0xceejay/2wd-diff-drive-bot/src/bot_description/meshes/tt_motor_3777_v10__3.stl

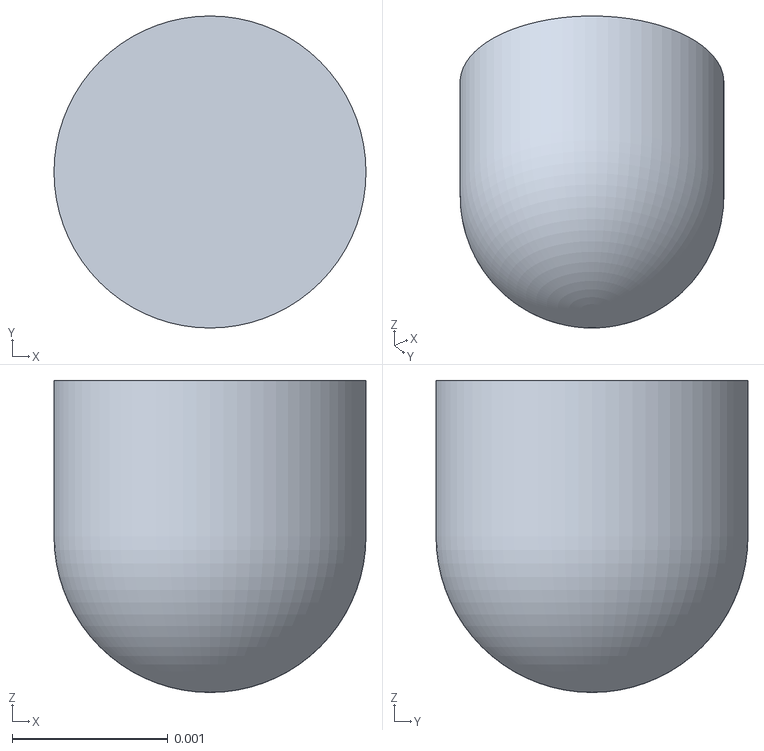
[picture p15: CAD file, 2026-05-07]
src/bot_description/meshes/tt_motor_3777_v10__3.stl
0.002 x 0.002 x 0.002
