0xceejay/2wd-diff-drive-bot/src/bot_description/meshes/tt_motor_3777_v10__2.stl

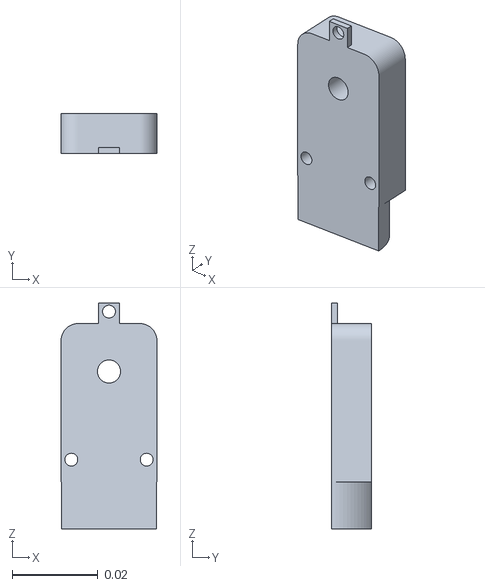
[picture p16: CAD file, 2026-05-07]
src/bot_description/meshes/tt_motor_3777_v10__2.stl
0.0224 x 0.0093 x 0.0528
