0xceejay/2wd-diff-drive-bot/src/bot_description/meshes/tt_motor_3777_v10__5.stl

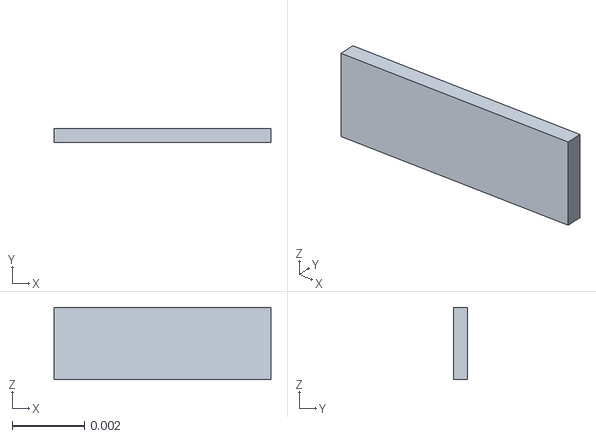
[picture p17: CAD file, 2026-05-07]
src/bot_description/meshes/tt_motor_3777_v10__5.stl
0.006 x 0.0004 x 0.002
