0xceejay/2wd-diff-drive-bot/src/bot_description/meshes/caster_40mm_wheel_support_01.stl

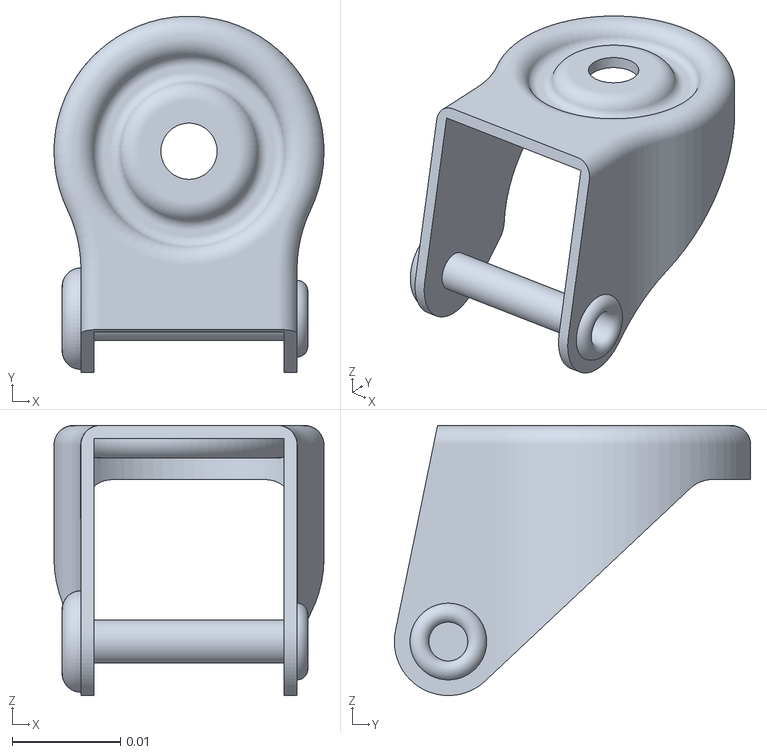
[picture p18: CAD file, 2026-05-07]
src/bot_description/meshes/caster_40mm_wheel_support_01.stl
0.025 x 0.033 x 0.025
