0xceejay/2wd-diff-drive-bot/src/bot_description/meshes/caster_40mm_swivel_plate_01.stl

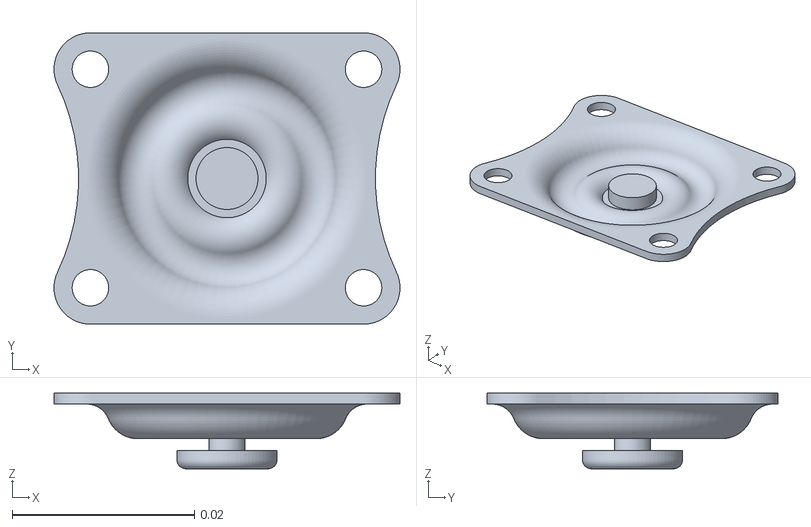
[picture p19: CAD file, 2026-05-07]
src/bot_description/meshes/caster_40mm_swivel_plate_01.stl
0.038 x 0.032 x 0.0083
