0xceejay/2wd-diff-drive-bot/src/bot_description/meshes/wheel.stl

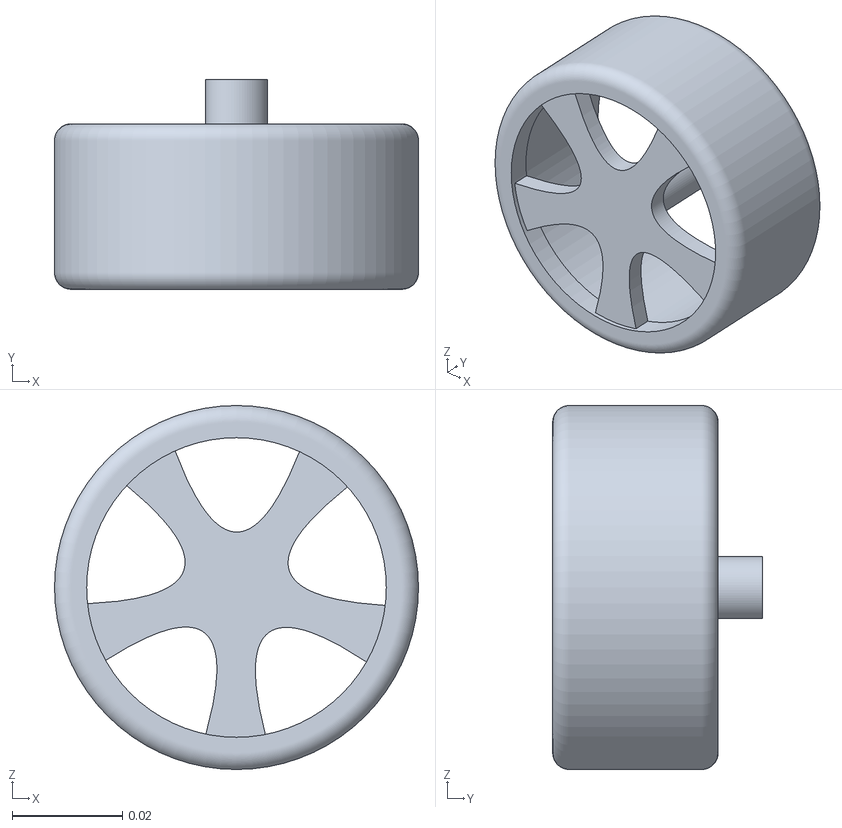
[picture p20: CAD file, 2026-05-07]
src/bot_description/meshes/wheel.stl
0.066 x 0.038 x 0.066
