0xceejay/2wd-diff-drive-bot/src/bot_description/meshes/tt_motor_3777_v10__8.stl

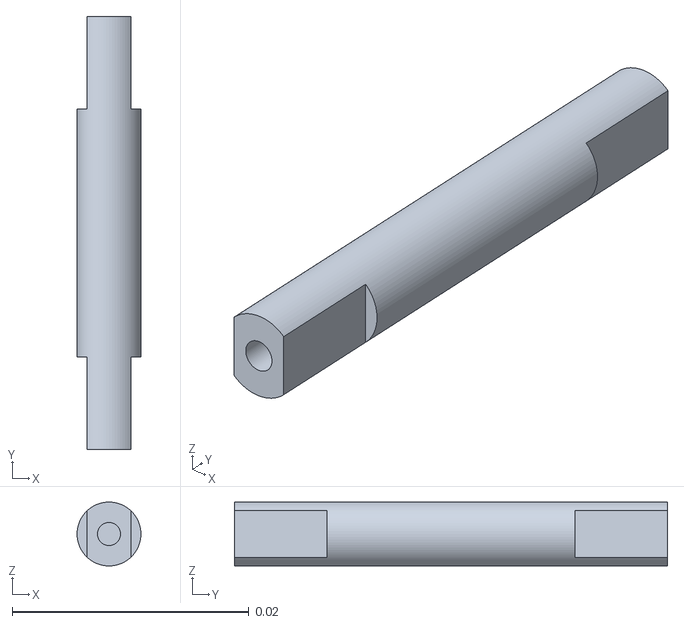
[picture p21: CAD file, 2026-05-07]
src/bot_description/meshes/tt_motor_3777_v10__8.stl
0.0054 x 0.0366 x 0.0054
