0xceejay/2wd-diff-drive-bot/src/bot_description/meshes/contacto_plano_v1_0.stl

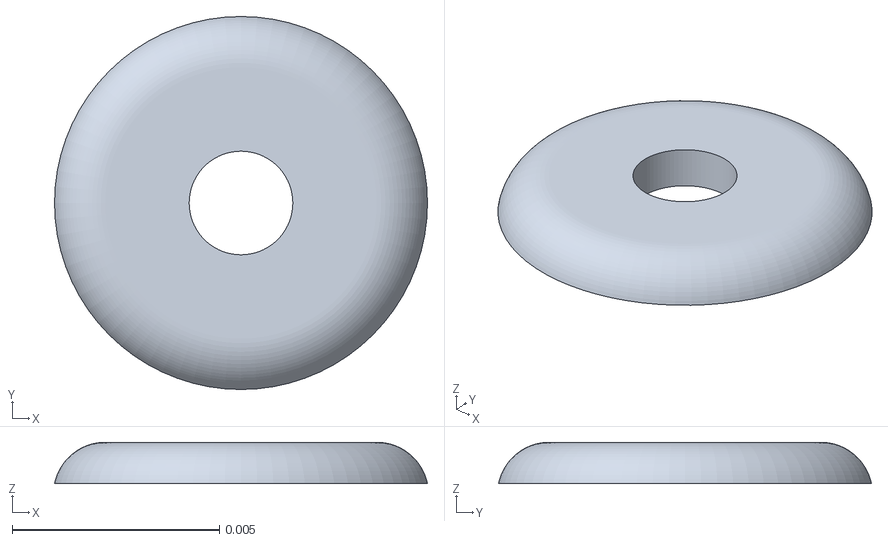
[picture p22: CAD file, 2026-05-07]
src/bot_description/meshes/contacto_plano_v1_0.stl
0.009 x 0.009 x 0.001
